yanataka60/PC-6001_SD/JPEG/ROM_DUMP(5).JPG

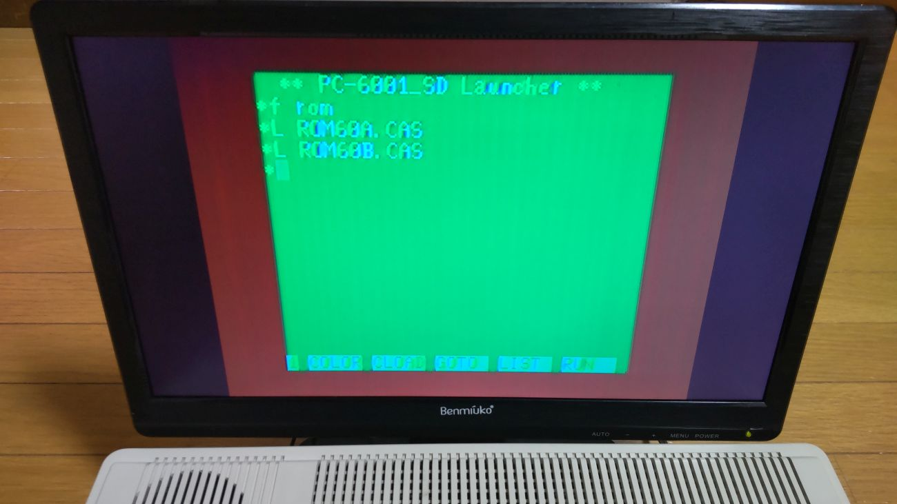
JPEG/ROM_DUMP(5).JPG
